Khajan352/FSO-Optical-Transceiver/simulation/receiver-stage-draft.asc

R1: res; 10K
R2: res; 10K
U1: OP747
V1: voltage; 9V
V2: voltage; SINE(0 5 50 0 0 0 25)
Named nets: 0
.tran 0.1
