Khajan352/FSO-Optical-Transceiver/simulation/transceiver.asc

R1: res; 10K
R2: res; 10K
R3: res; 10K
R4: res; 10K
R5: res; 10K
R6: res; 10K
R7: res; 5.1K
R8: res; 10K
U1: OP747
U2: 4N25
U3: OP747
U4: OP747
V1: voltage; 5V
V2: voltage; SINE(0 3.3 100 0 0 0 50)
V3: voltage; 9V
V4: voltage; 9V
V5: voltage; 9V
V6: voltage; 9V
Named nets: Output, 0
.tran 0.1
TRANSMITTER
RECEIVER
